jochen-rath/rfidLmsSteuerung/micropython_modules/wlan.py

def wlan_connect(ssid='zugang', password='passwort'):
    import network
    wlan = network.WLAN(network.STA_IF)
    if not wlan.active() or not wlan.isconnected():
        wlan.active(True)
        print('connecting to:', ssid)
        wlan.connect(ssid, password)
        while not wlan.isconnected():
            pass
    print('network config:', wlan.ifconfig())

wlan_connect()
